Felteshobbies/SimGliderControl/docs/images/s2-4.jpg

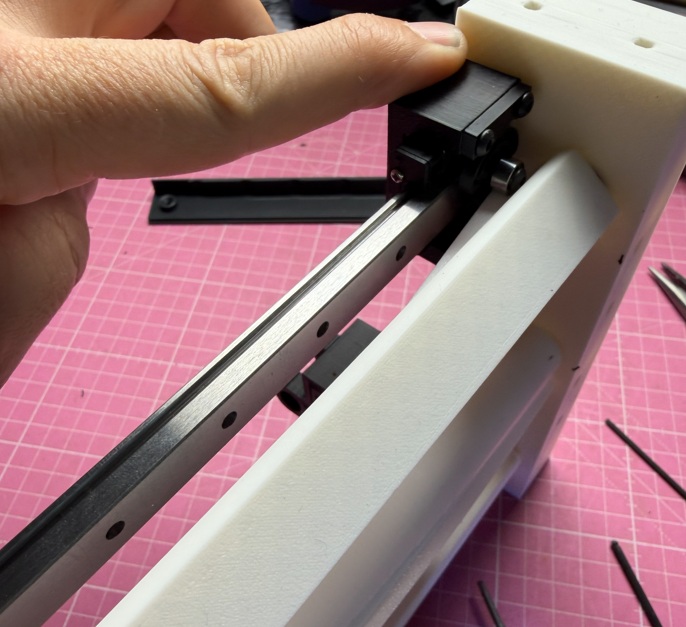
docs/images/s2-4.jpg
