Felteshobbies/SimGliderControl/docs/images/s2-8.jpg

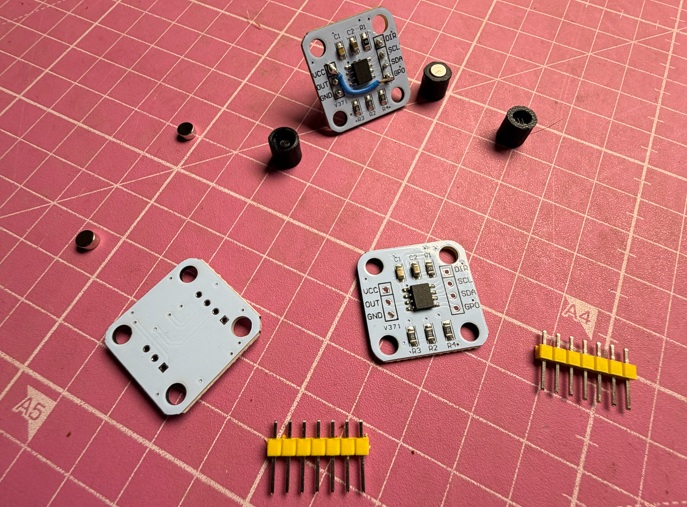
docs/images/s2-8.jpg
