Felteshobbies/SimGliderControl/docs/images/s3-2.jpg

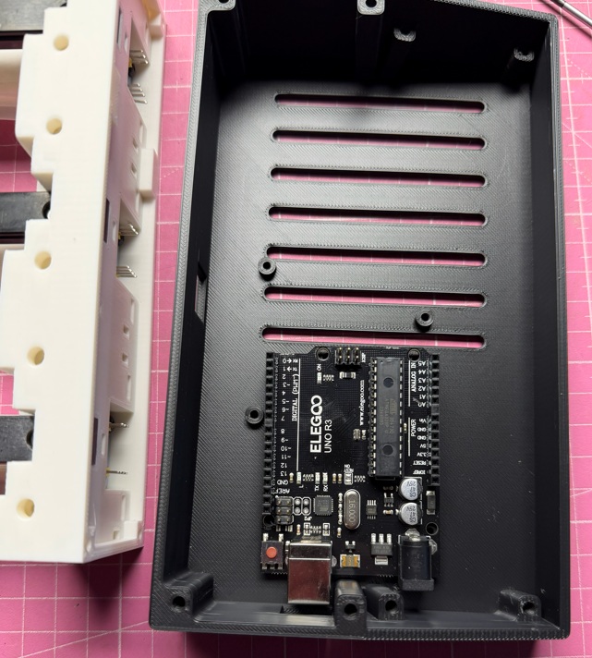
docs/images/s3-2.jpg
