Felteshobbies/SimGliderControl/docs/images/s4-1.jpg

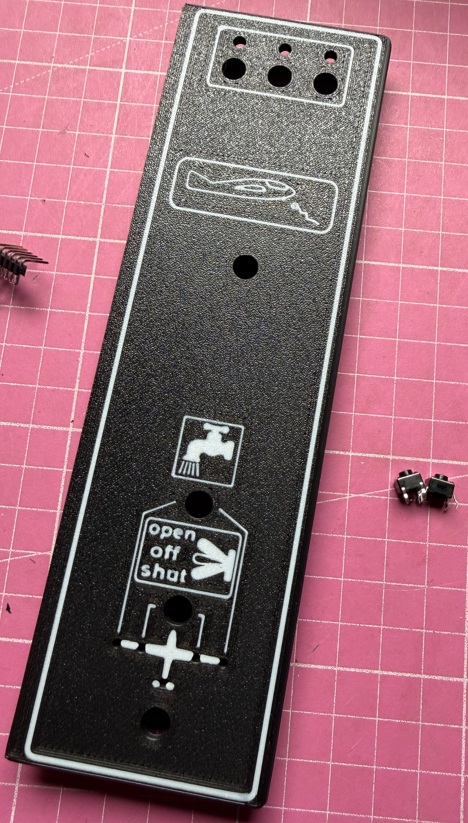
docs/images/s4-1.jpg
