Felteshobbies/SimGliderControl/Step3/GliderCtrEnclosureAux_v1-Enclosure.3mf

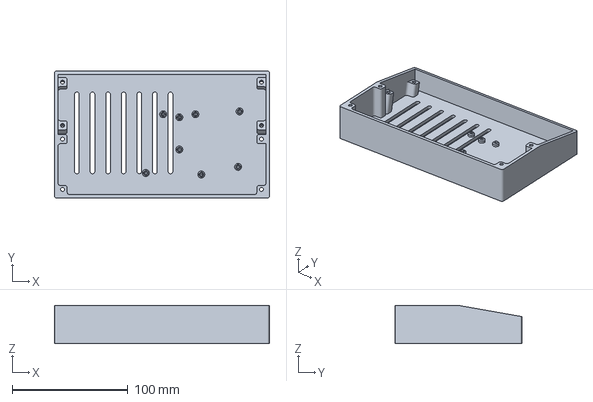
[picture p21: CAD file, 2026-01-27]
Step3/GliderCtrEnclosureAux_v1-Enclosure.3mf
186.0 x 110.0 x 33.0 mm
