Felteshobbies/SimGliderControl/Step4/GliderCtrPanel_v1-FlapsSpoiler.step

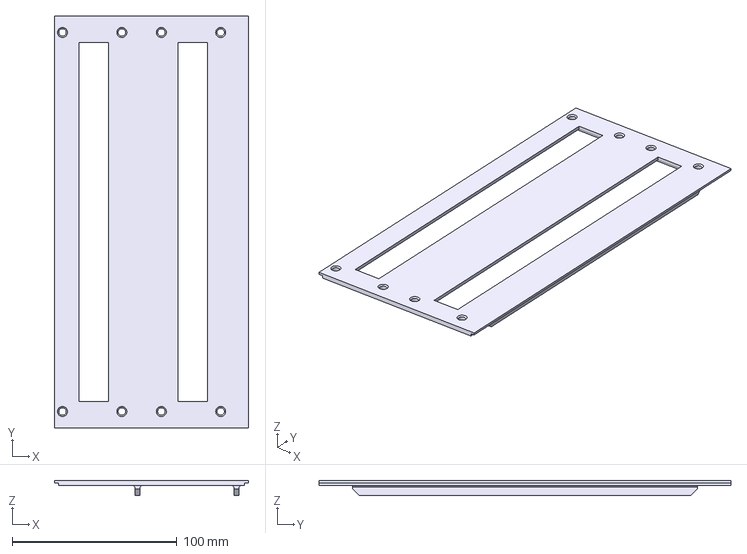
[picture p22: CAD file, 2026-01-27]
Step4/GliderCtrPanel_v1-FlapsSpoiler.step
118.0 x 250.0 x 9.00 mm
