Felteshobbies/SimGliderControl/Step5/GliderCtrlHandles_v1-WinchRelease.step

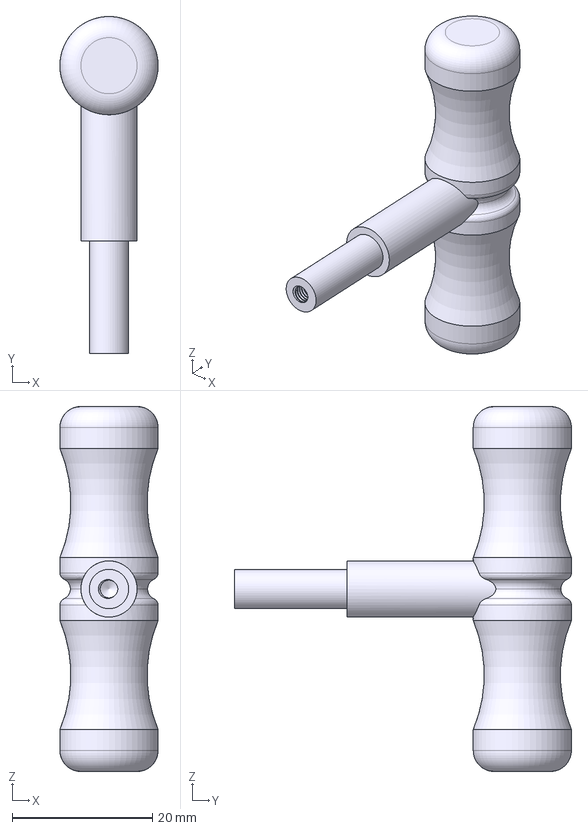
[picture p23: CAD file, 2026-01-27]
Step5/GliderCtrlHandles_v1-WinchRelease.step
14.0 x 48.0 x 52.0 mm
