Felteshobbies/SimGliderControl/Step1/GliderCtrBase_v1-GuideShaft.step

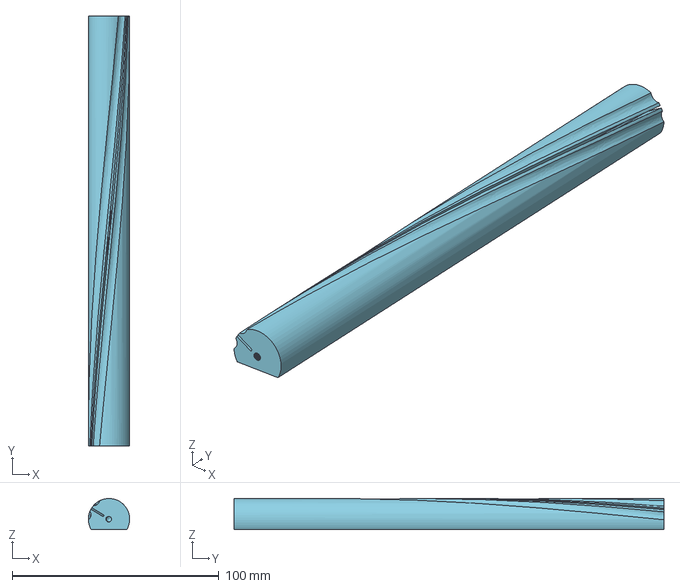
[picture p24: CAD file, 2026-01-27]
Step1/GliderCtrBase_v1-GuideShaft.step
20.0 x 208.0 x 15.0 mm
