Felteshobbies/SimGliderControl/Step2/GliderCtrCarriage_v1-HandleMount.3mf

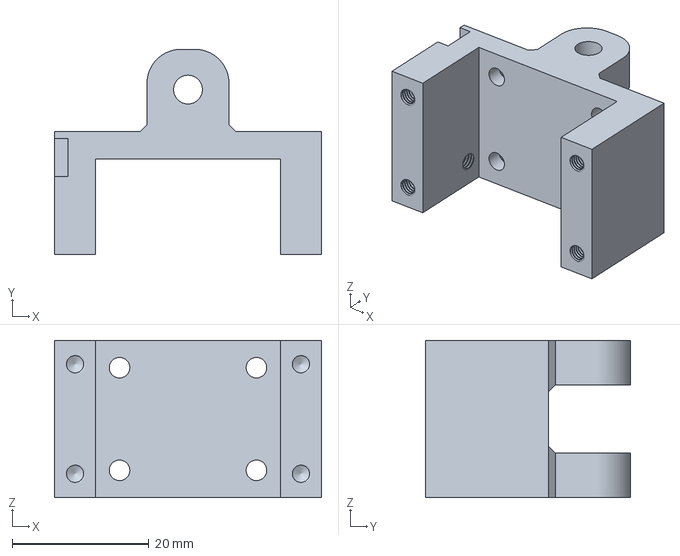
[picture p25: CAD file, 2026-01-27]
Step2/GliderCtrCarriage_v1-HandleMount.3mf
39.0 x 30.0 x 23.0 mm
