Felteshobbies/SimGliderControl/Step4/GliderCtrPanel_v1-front.step

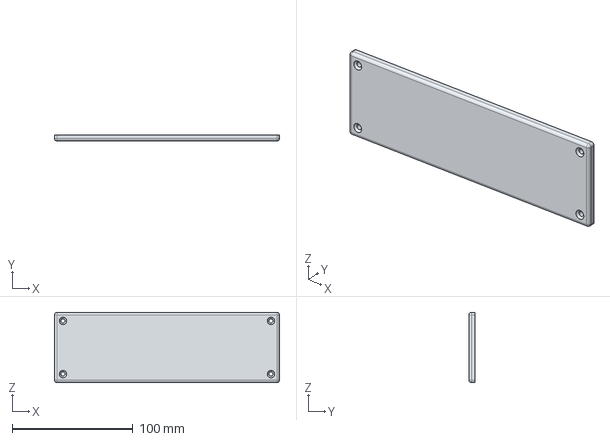
[picture p26: CAD file, 2026-01-27]
Step4/GliderCtrPanel_v1-front.step
186.0 x 5.00 x 58.0 mm
