Felteshobbies/SimGliderControl/Step2/GliderCtrCarriage_v1-KnobMount.3mf

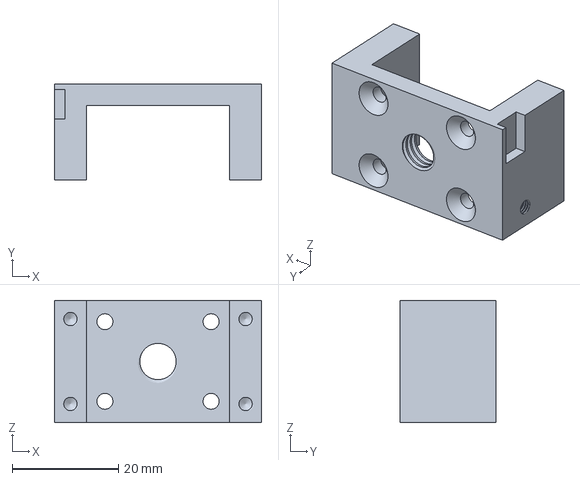
[picture p27: CAD file, 2026-01-27]
Step2/GliderCtrCarriage_v1-KnobMount.3mf
39.0 x 18.0 x 23.0 mm
