Felteshobbies/SimGliderControl/Step4/GliderCtrPanel_v1-Trim.step

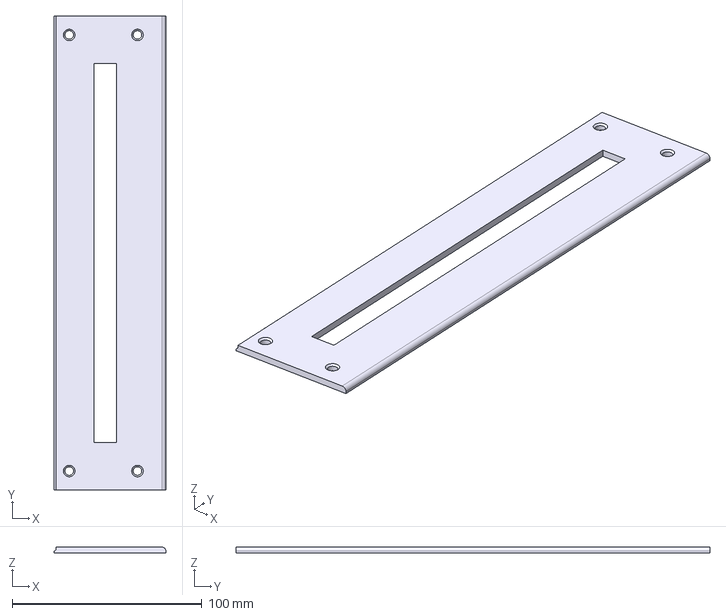
[picture p28: CAD file, 2026-01-27]
Step4/GliderCtrPanel_v1-Trim.step
59.0 x 250.0 x 3.00 mm
