Felteshobbies/SimGliderControl/Step5/GliderCtrlHandles_v1-WinchReleaseMount.step

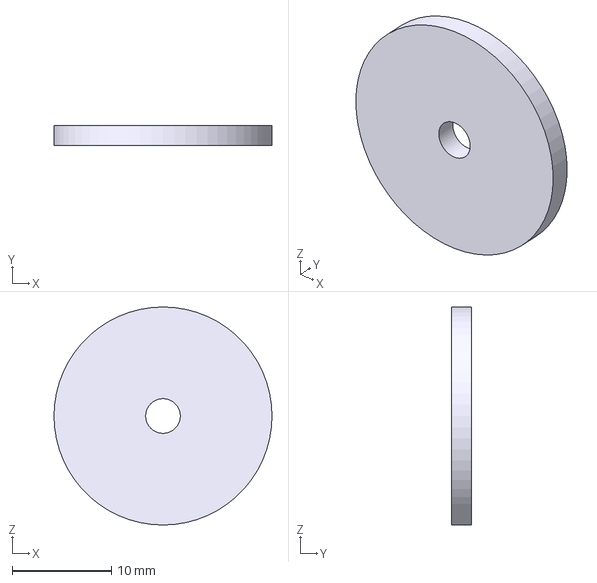
[picture p29: CAD file, 2026-01-27]
Step5/GliderCtrlHandles_v1-WinchReleaseMount.step
22.0 x 2.00 x 22.0 mm
