Felteshobbies/SimGliderControl/Step4/GliderCtrPanel_v1-ScaleAS33.step

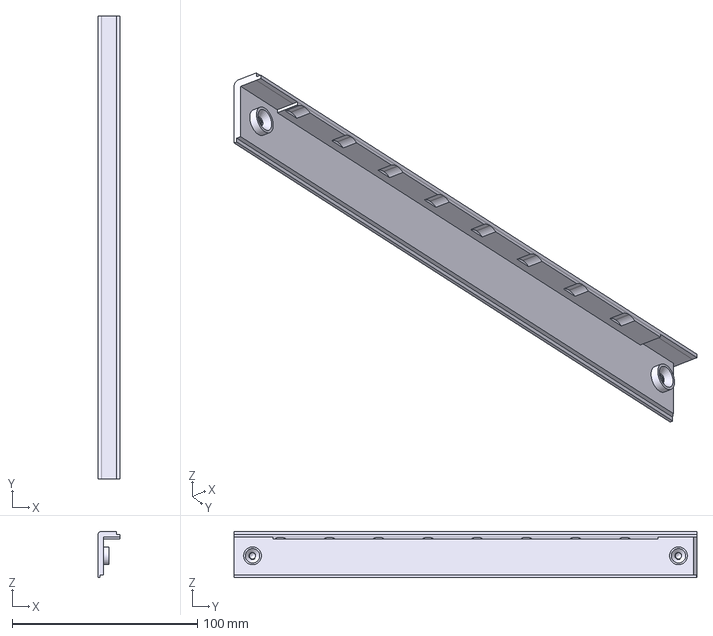
[picture p30: CAD file, 2026-01-27]
Step4/GliderCtrPanel_v1-ScaleAS33.step
12.0 x 250.0 x 25.0 mm
