Felteshobbies/SimGliderControl/Step5/GliderCtrlHandles_v1-TrimFlap.step

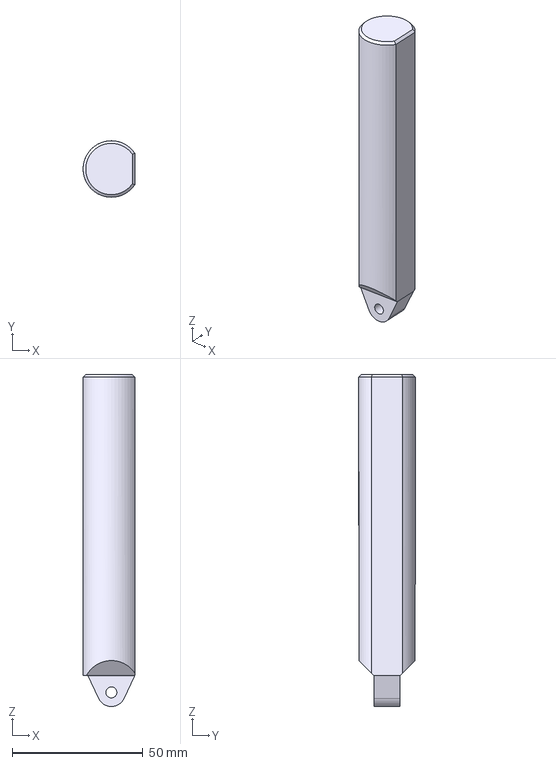
[picture p31: CAD file, 2026-01-27]
Step5/GliderCtrlHandles_v1-TrimFlap.step
19.8 x 21.6 x 126.9 mm
