Felteshobbies/SimGliderControl/Step4/GliderCtrPanel_v1-Top.step

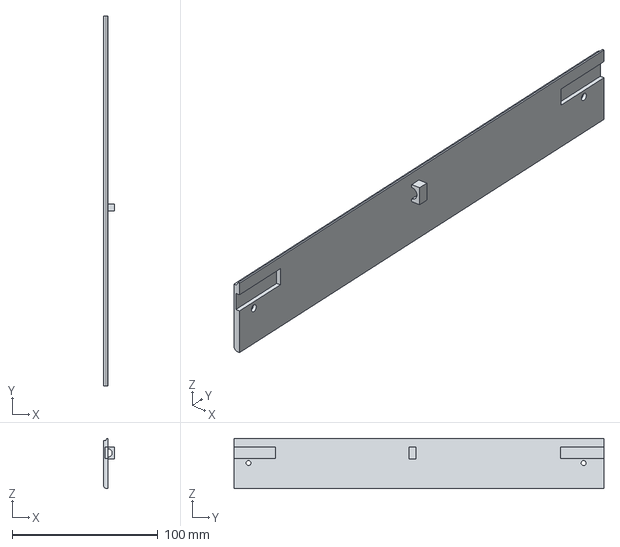
[picture p32: CAD file, 2026-01-27]
Step4/GliderCtrPanel_v1-Top.step
7.32 x 254.0 x 34.4 mm
